xeenoon/Thermoscanatron/3d/TOP_part2.stl

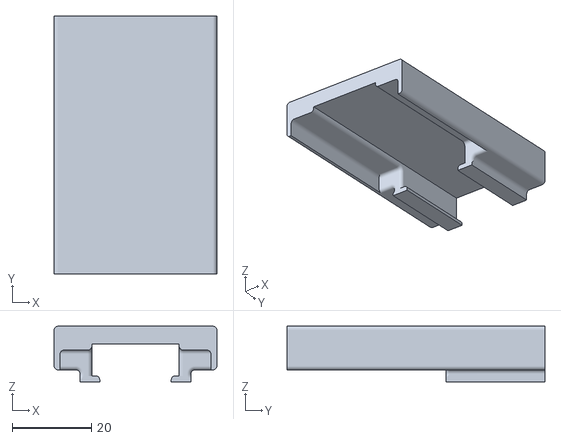
[picture p7: CAD file, 2026-10-03]
3d/TOP_part2.stl
41.0 x 65.0 x 14.0
