xeenoon/Thermoscanatron/3d/TOP_part1.1.step

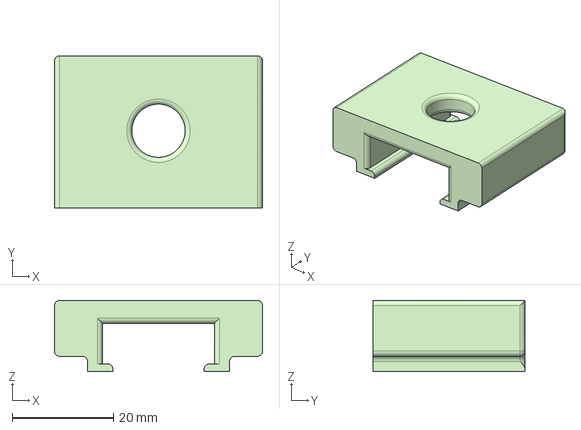
[picture p8: CAD file, 2026-10-03]
3d/TOP_part1.1.step
41.0 x 30.0 x 14.0 mm
