xeenoon/Thermoscanatron/3d/bottom+ phone_attachment_version_2.3mf

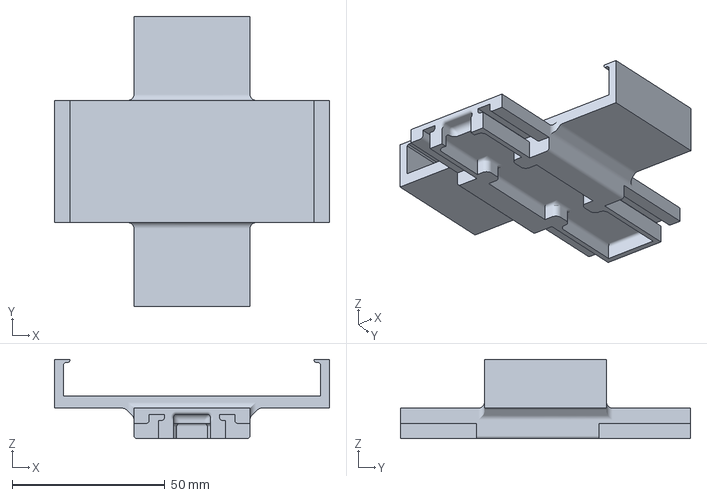
[picture p10: CAD file, 2026-10-03]
3d/bottom+ phone_attachment_version_2.3mf
90.0 x 95.0 x 26.0 mm
