xeenoon/Thermoscanatron/3d/Adafruit_5700_QT_Py_S3_keepout_preview.stl

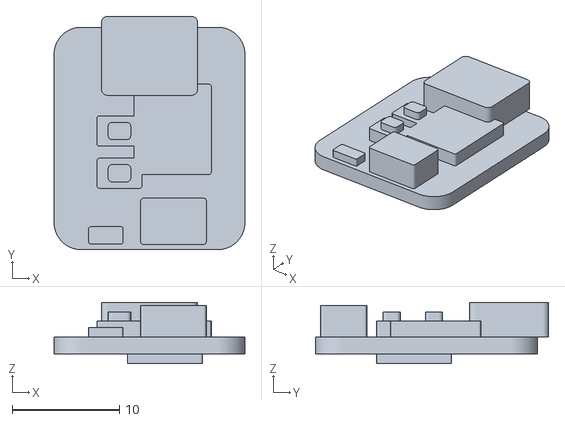
[picture p11: CAD file, 2026-10-03]
3d/Adafruit_5700_QT_Py_S3_keepout_preview.stl
17.8 x 21.7 x 5.70
