xeenoon/Thermoscanatron/3d/trial2HACKATHON.3mf

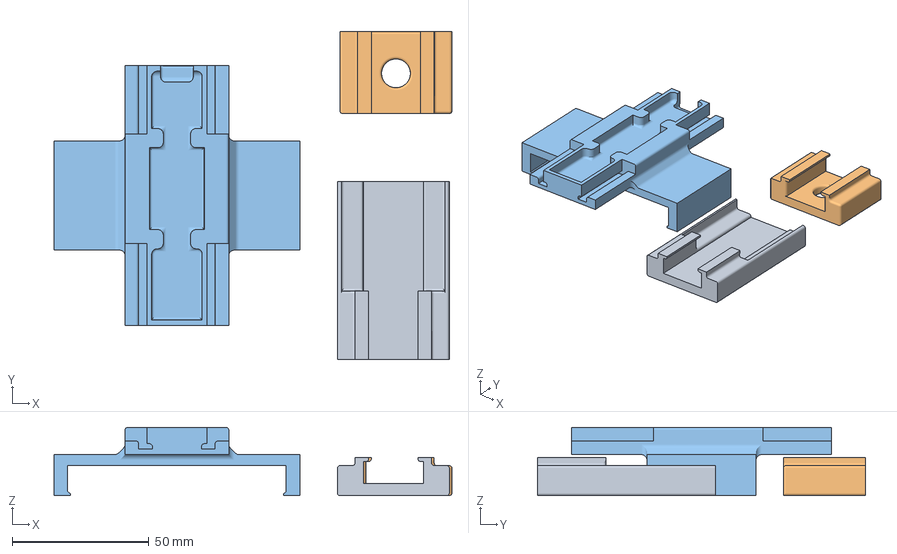
[picture p12: CAD file, 2026-10-03]
3d/trial2HACKATHON.3mf
145.7 x 119.9 x 25.0 mm
TOPp2.stl
TOPp1.stl
bottom+ phone attachment (2).stl
