xeenoon/Thermoscanatron/3d/XIAO_ESP32S3_v1.1_Dimensioning.dxf

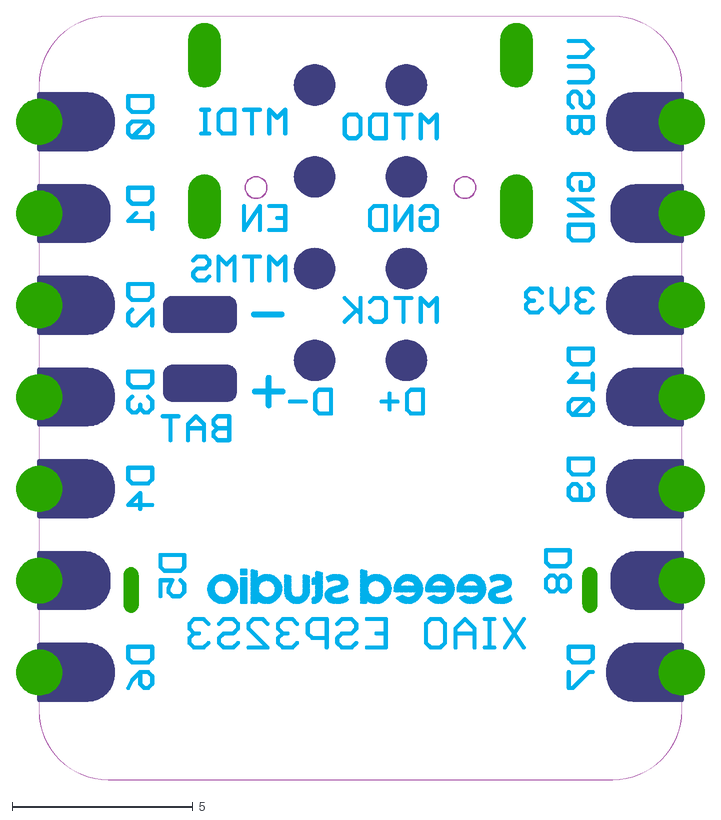
[picture p13: CAD file, 2026-10-03]
3d/XIAO_ESP32S3_v1.1_Dimensioning.dxf
19.0 x 21.1
