xeenoon/Thermoscanatron/3d/TOP.step

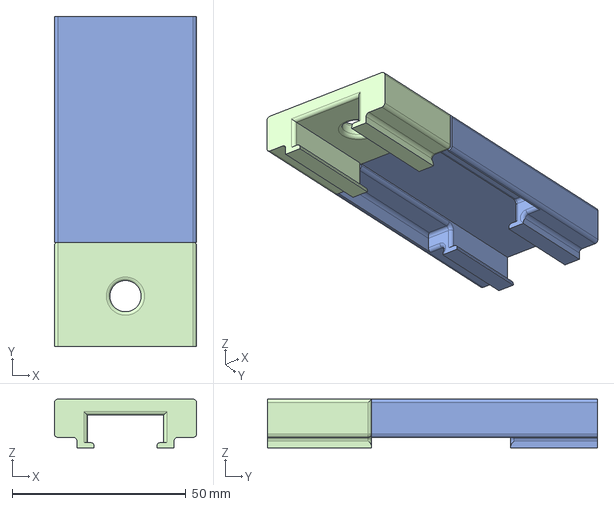
[picture p14: CAD file, 2026-10-03]
3d/TOP.step
41.0 x 95.0 x 14.0 mm
