xeenoon/Thermoscanatron/3d/bottom+ phone attachment.step

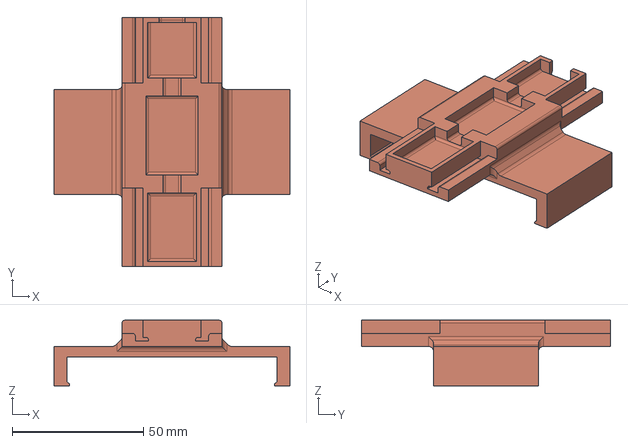
[picture p15: CAD file, 2026-10-03]
3d/bottom+ phone attachment.step
90.0 x 95.0 x 25.0 mm
