xeenoon/Thermoscanatron/3d/INSERT_DIRECTLY_JST_SH_4pin_CONNECTOR_PAIR.step

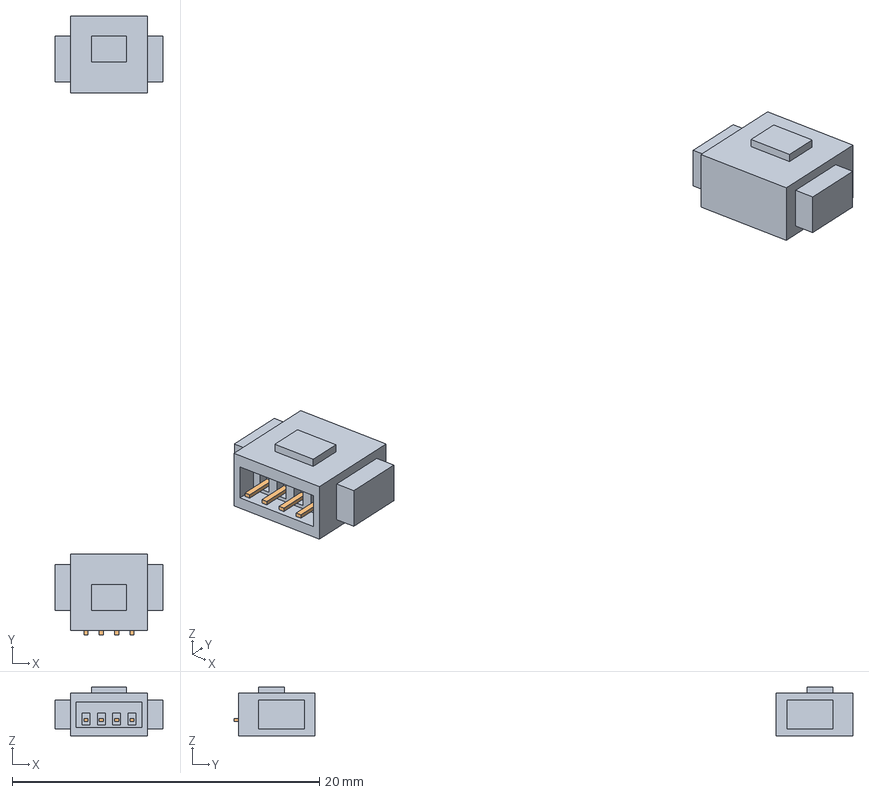
[picture p16: CAD file, 2026-10-03]
3d/INSERT_DIRECTLY_JST_SH_4pin_CONNECTOR_PAIR.step
7.00 x 40.3 x 3.18 mm
