xeenoon/Thermoscanatron/3d/INSERT_DIRECTLY_JST_SH_4pin_30mm_WIRES.step

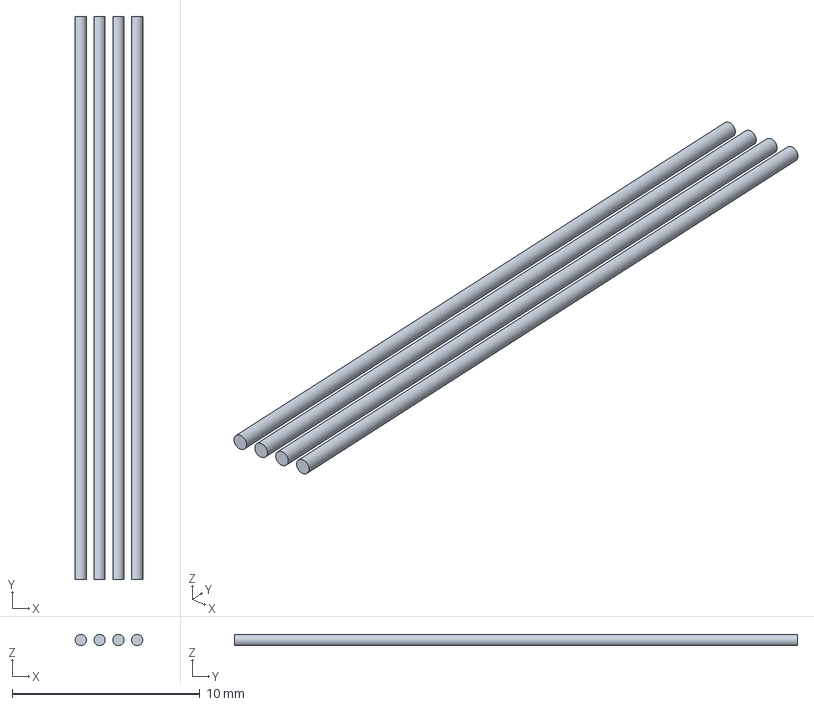
[picture p17: CAD file, 2026-10-03]
3d/INSERT_DIRECTLY_JST_SH_4pin_30mm_WIRES.step
3.60 x 30.0 x 0.6 mm
