xeenoon/Thermoscanatron/3d/JST_SH_4pin_STEMMA_QT_50mm_cable_robust.step

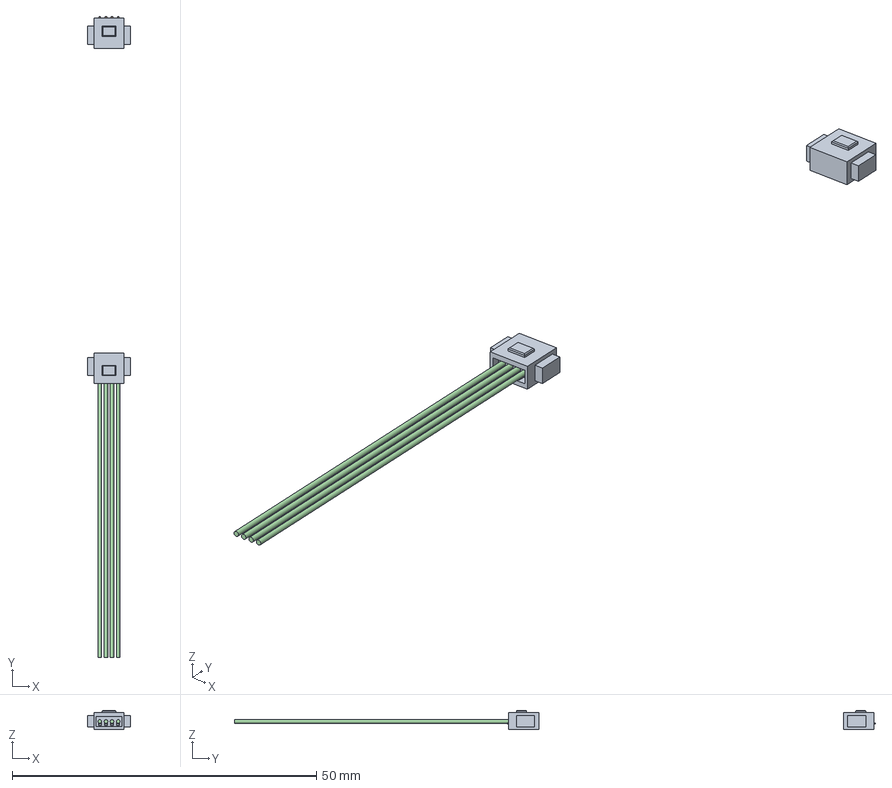
[picture p18: CAD file, 2026-10-03]
3d/JST_SH_4pin_STEMMA_QT_50mm_cable_robust.step
7.00 x 105.3 x 3.18 mm
